lan-ensad/SplitFlap/_mod/_renders/02.jpg

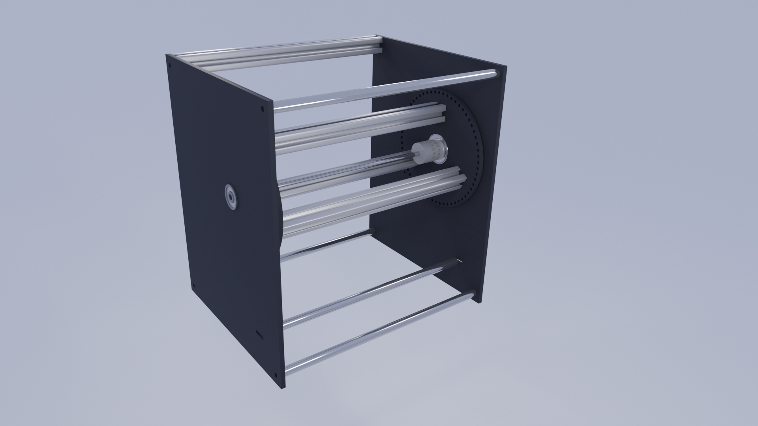
_mod/_renders/02.jpg
